AliShug/HeadSLAM/reference/cable_attach.jpg

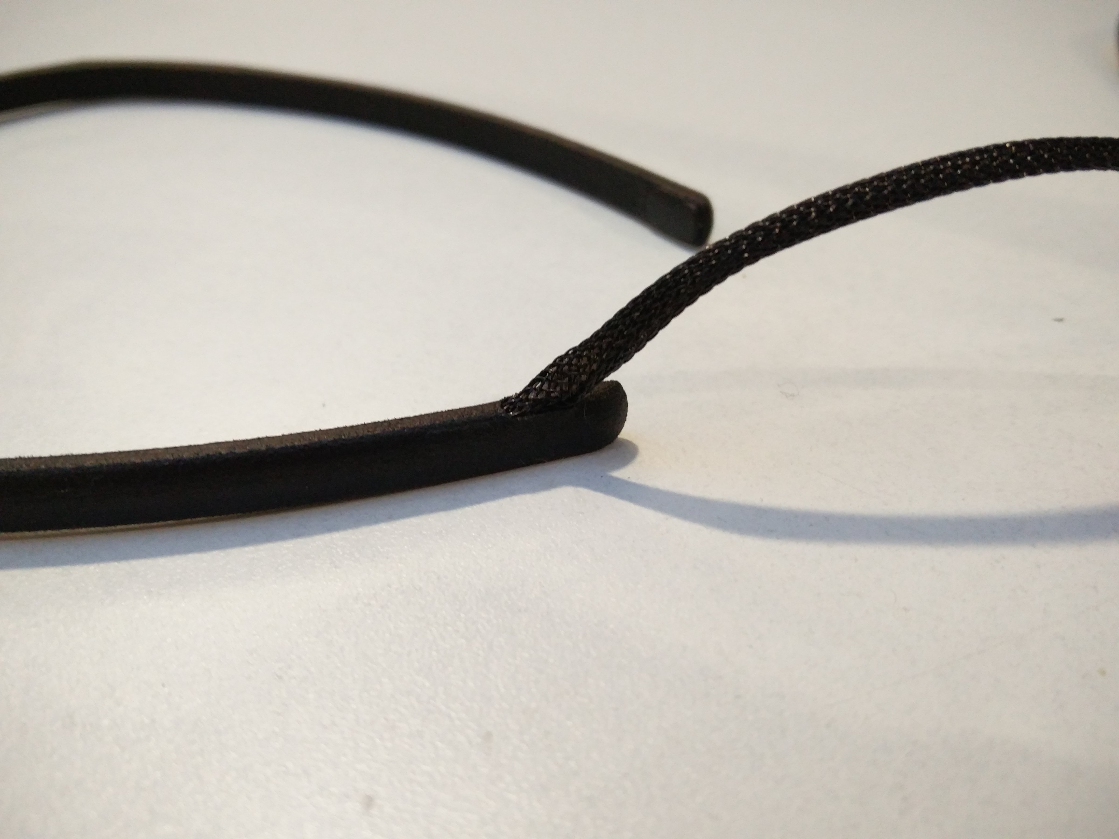
reference/cable_attach.jpg
