AliShug/HeadSLAM/reference/camera.jpg

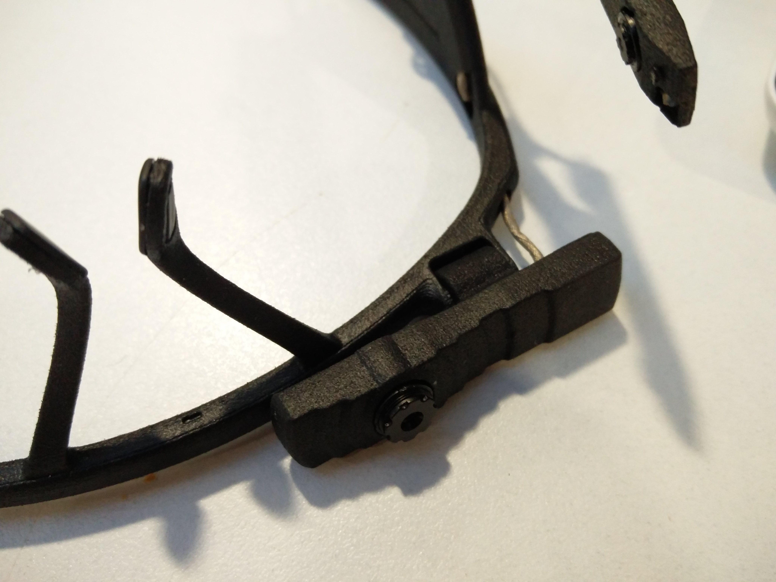
reference/camera.jpg
