AliShug/HeadSLAM/reference/eye-tracker_2.jpg

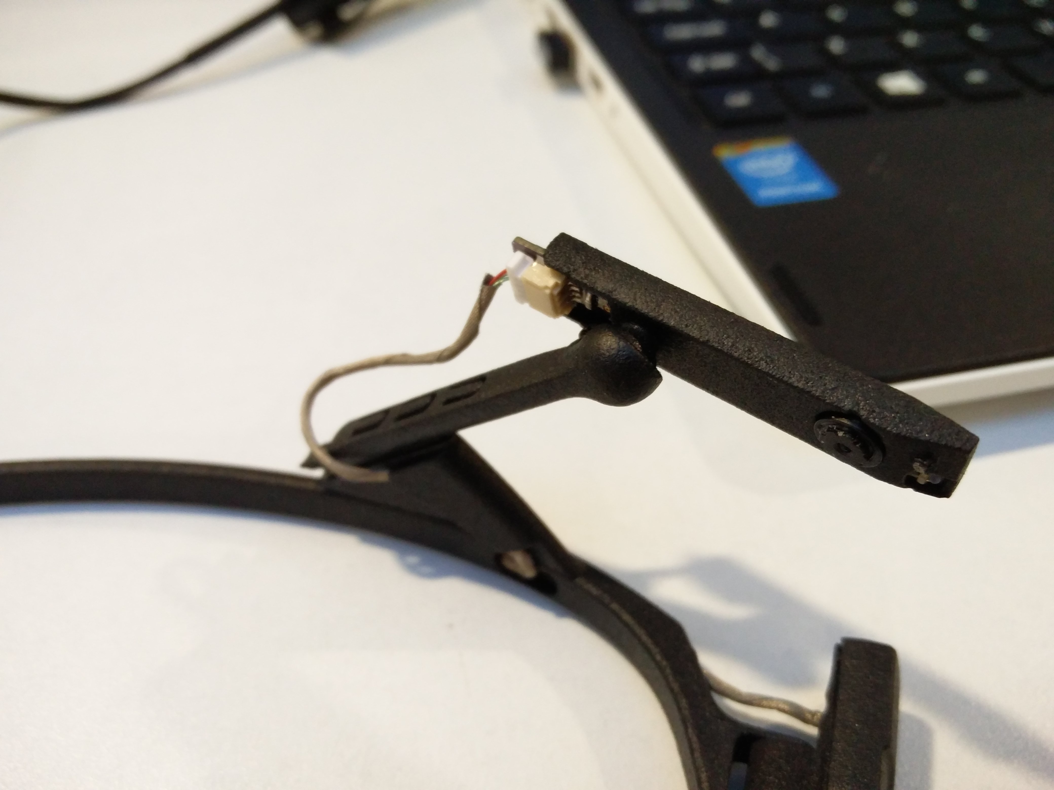
reference/eye-tracker_2.jpg
