AliShug/HeadSLAM/reference/ir_in_mounting.jpg

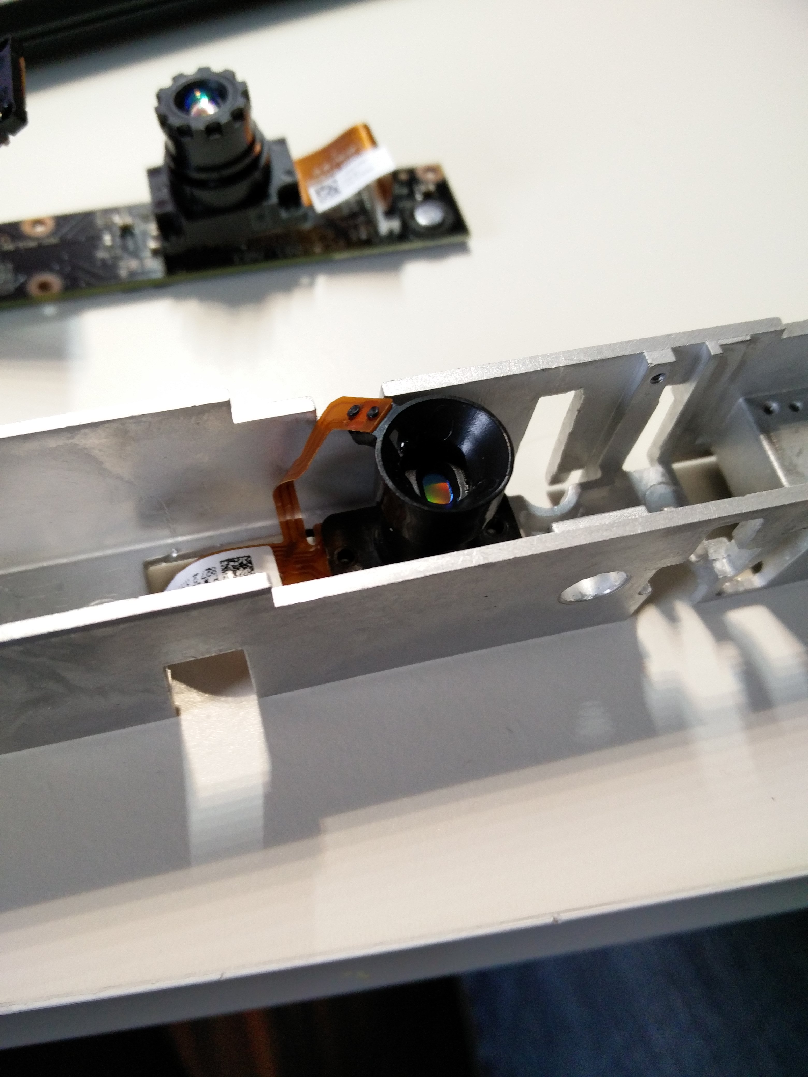
reference/ir_in_mounting.jpg
