AliShug/HeadSLAM/reference/rest_front.jpg

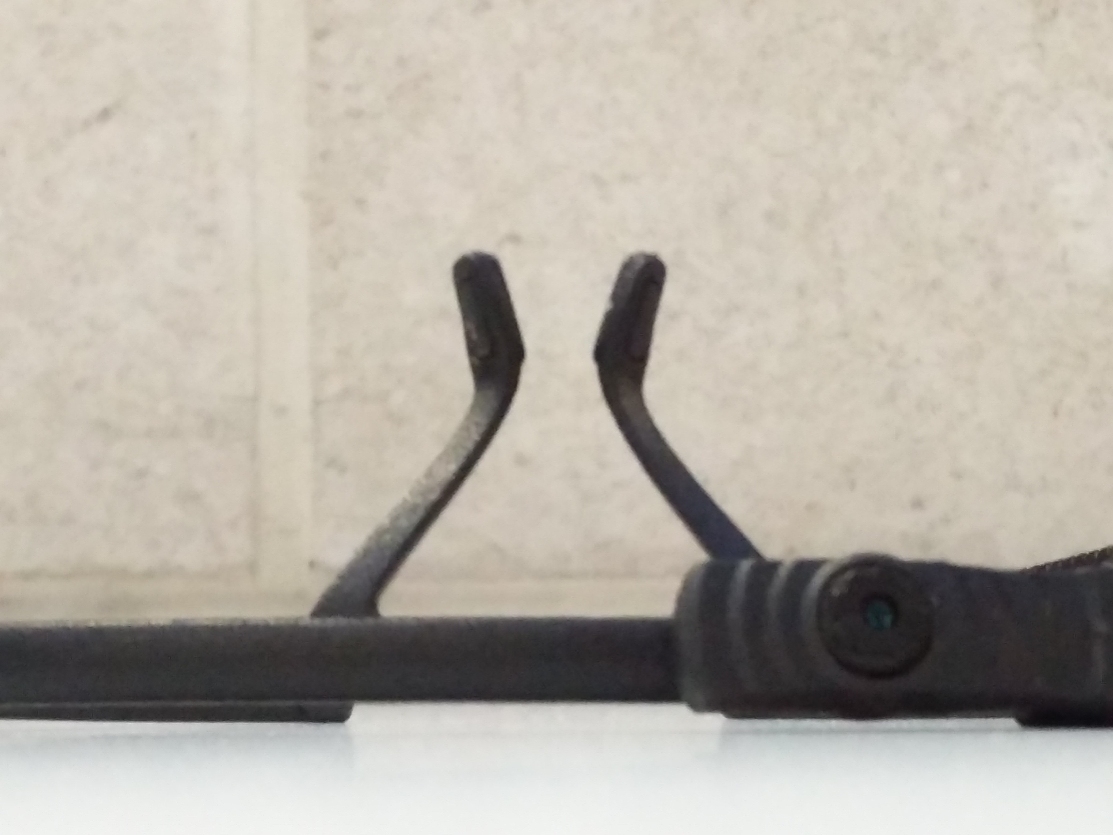
reference/rest_front.jpg
