AliShug/HeadSLAM/reference/rest_front_2.jpg

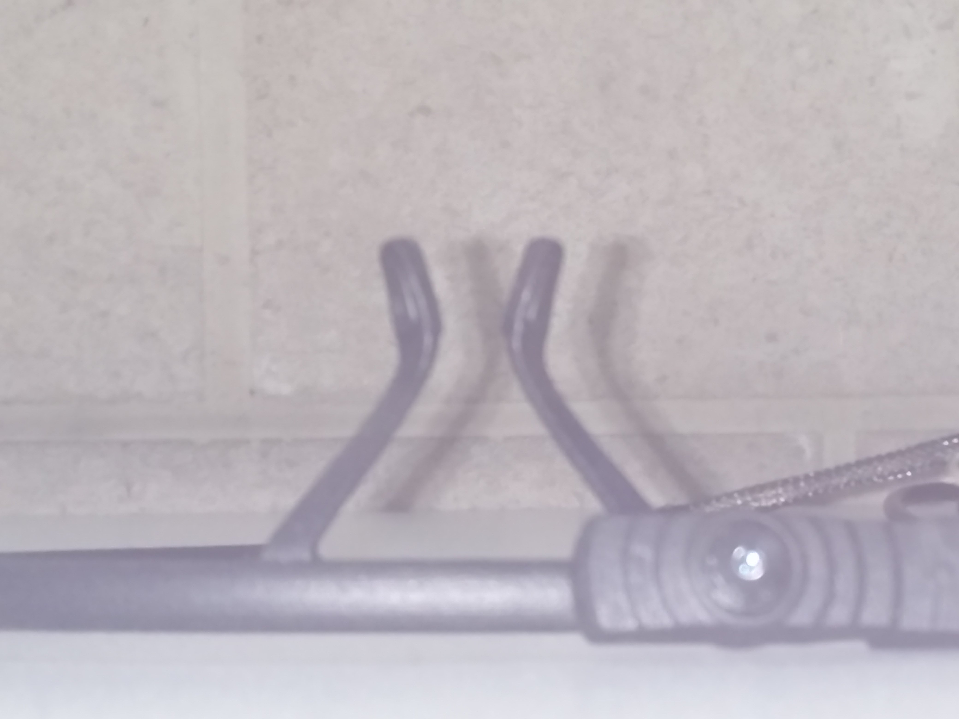
reference/rest_front_2.jpg
