AliShug/HeadSLAM/reference/rest_pads_2.jpg

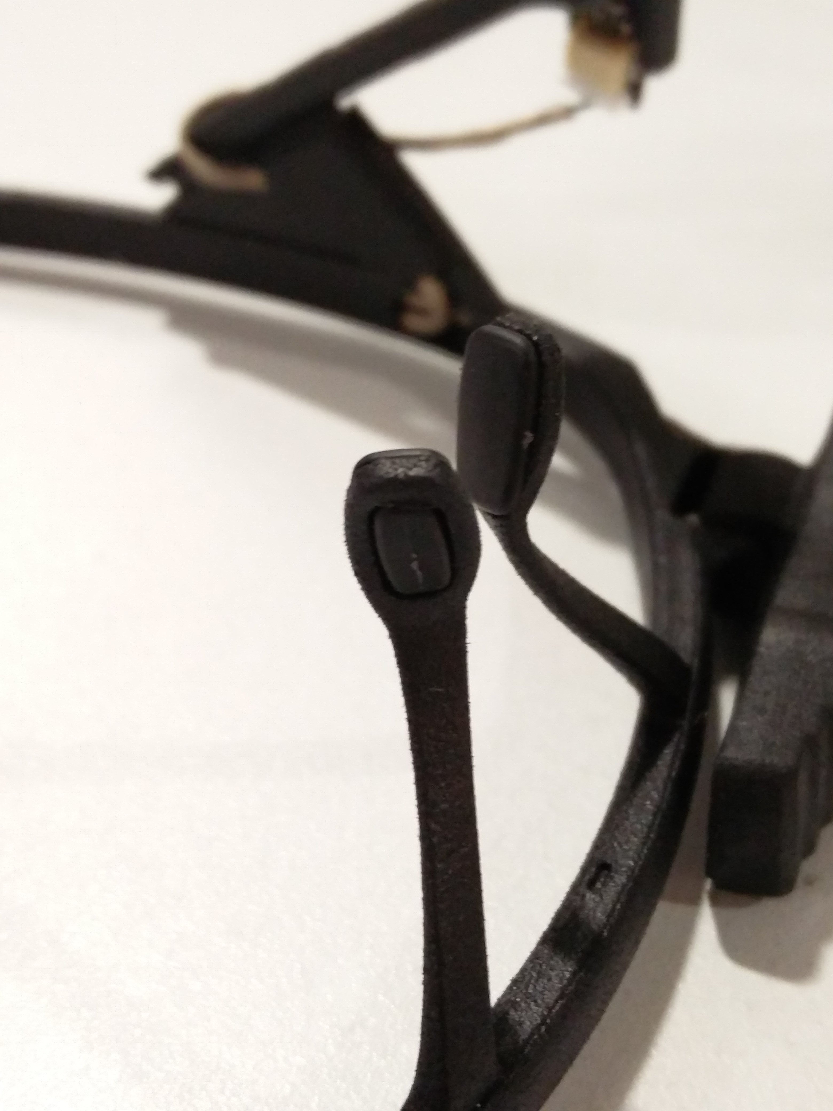
reference/rest_pads_2.jpg
