AliShug/HeadSLAM/reference/rest_side_2.jpg

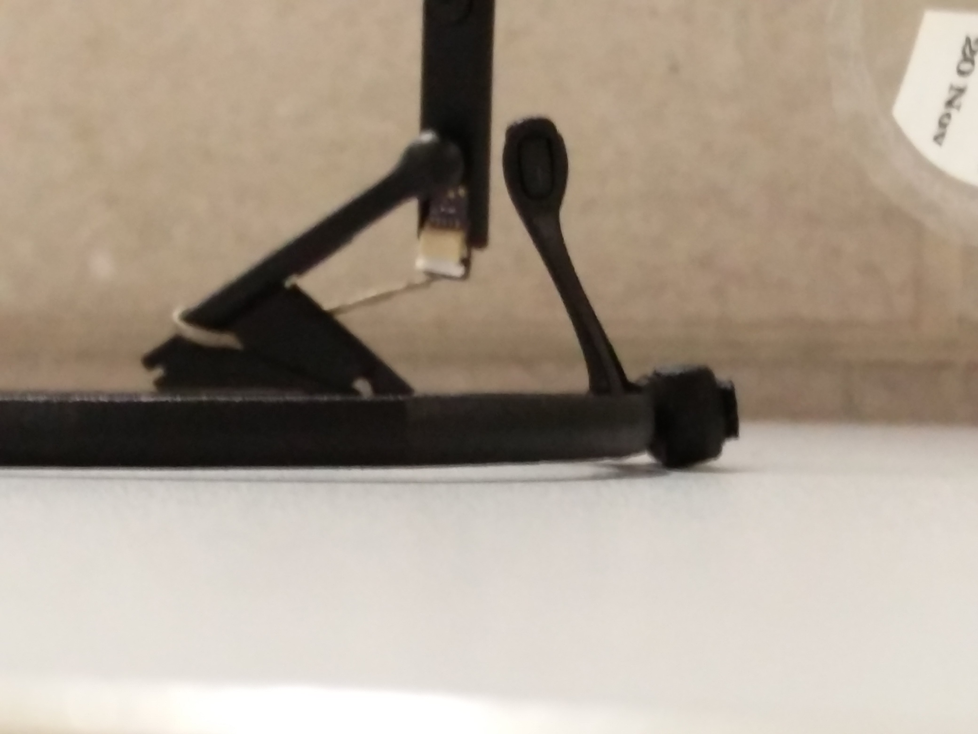
reference/rest_side_2.jpg
