AliShug/HeadSLAM/reference/xtion_pcb.jpg

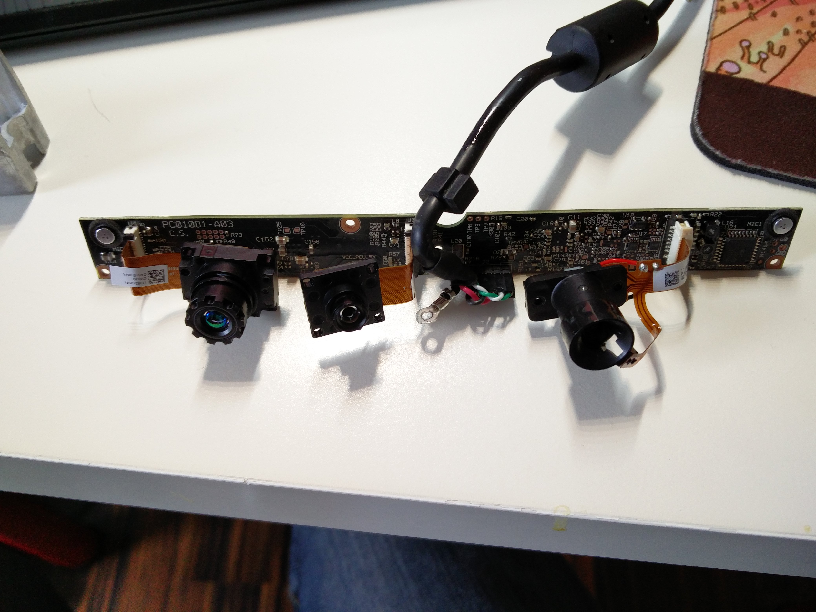
reference/xtion_pcb.jpg
